MOSH-Insa-Toulouse/5ISS_Hatibi_Anka/LTSpice/Ampli.asc

C1: cap; 100n
C2: cap; 100n
C3: cap; 100n
C4: cap; 1µ
C5: cap; 1p
R1: res; 100k
R2: res; 1k
R3: res; 100k
R4: res; 1k
R5: res; 10k
U1: LTC1050
V1: voltage; 5
V2: voltage; PULSE(50n 100n 1 0.1 0.1 2); AC 1 0
V3: voltage; PULSE(0 1 0.2 0.1 0.1 20)
X1: capteur
Named nets: 0, Vcc, ADC
.tran 0 2 0 10m
;op
;ac dec 100 0.01 100Meg
.param G0=10n
.param G1=10n
