MOSH-Insa-Toulouse/5ISS_Hatibi_Anka/LTSpice/capteur.asc

B1: bi; I=V(cp,cn)*(10n+(V(gc,gn)*10n))
C1: cap; 200µ
R1: res; 1k
Named nets: cp, cn, gp, gn, gc
